thomasfredericks/Mozard/extras/Max (Cycling '74)/Control Mozard with MIDI through serial.png

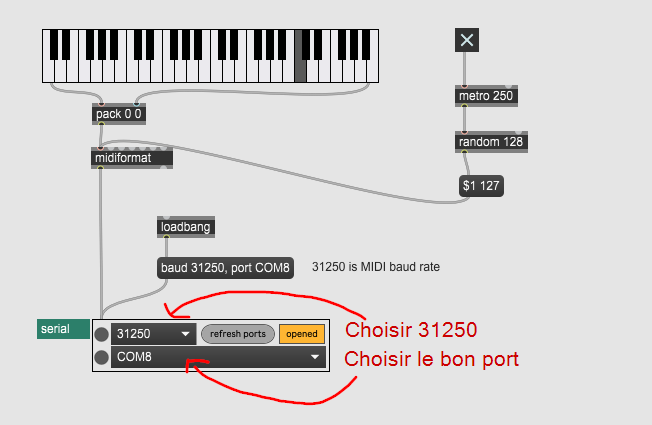
extras/Max (Cycling '74)/Control Mozard with MIDI through serial.png
