thomasfredericks/Mozard/src/Mozard.h

// ATMEL ATMEGA8 & 168 / ARDUINO
//
//                  +-\/-+
//            PC6  1|    |28  PC5 (AI 5)
//      (D 0) PD0  2|    |27  PC4 (AI 4)
//      (D 1) PD1  3|    |26  PC3 (AI 3)
//      (D 2) PD2  4|    |25  PC2 (AI 2)
// PWM+ (D 3) PD3  5|    |24  PC1 (AI 1)
//      (D 4) PD4  6|    |23  PC0 (AI 0)
//            VCC  7|    |22  GND
//            GND  8|    |21  AREF
//            PB6  9|    |20  AVCC
//            PB7 10|    |19  PB5 (D 13)
// PWM+ (D 5) PD5 11|    |18  PB4 (D 12)
// PWM+ (D 6) PD6 12|    |17  PB3 (D 11) PWM
//      (D 7) PD7 13|    |16  PB2 (D 10) PWM
//      (D 8) PB0 14|    |15  PB1 (D 9) PWM
//                  +----+
//


// POTS
// A1, A6, A7

// PIANO PADS
// A5, A4, A3, A2, D12, D11, D8, D7, D6, D5, D4, D3

// BUTTON 
// D2

/*
    IMPORTANT: Mozard requires mozzi_config.h to be
    be changed from STANDARD mode to HIFI.
    In Mozz/mozzi_config.h, change
    #define AUDIO_MODE STANDARD
    //#define AUDIO_MODE HIFI
    to
    //#define AUDIO_MODE STANDARD
    #define AUDIO_MODE HIFI

*/

#ifndef MOZARD_TOUCH_SENSITIVITY
#define MOZARD_TOUCH_SENSITIVITY 2
#endif


// powers of 2 please
#define CONTROL_RATE 256

#include <mozzi_midi.h>
/*
#ifndef NOMIDI

#include <MIDI.h>
MIDI_CREATE_DEFAULT_INSTANCE();

#endif
*/

#include "MozziGuts.h"
#include "mozzi_rand.h"

#include "MozardMidi.h"


class MozardNano {

  public:

    /*
        int findHighestKeyHeld() {
          int key = -1;
          for ( uint8_t i = 0; i < 12; i++ ) {
            if ( keys[i] > 0 ) key = i;
          }
          return key;
        }
    */
  private:

    MozardMidi midi = MozardMidi(&Serial);
   

    bool keys[14]; // 12 keys + 2 buttons

    uint8_t keyPins[14] = {A5, A4, A3, A2, 12, 11, 8, 7, 6, 5, 4, 3,2,A0};
    uint8_t thresholds[14] = {0, 0, 0, 0, 0, 0, 0, 0, 0, 0, 0, 0, 0,0};
    uint8_t keyIndex = 0;
    uint8_t keyJustPressed = 0;
    uint8_t keyJustReleased = 0;
    uint8_t buttonJustPressed = 0;

    char octave = 5;

    byte analogReading = 0;
    #define MOZARD_ANALOG_PINS 3
    int analogValues[MOZARD_ANALOG_PINS];
    byte analogPins[MOZARD_ANALOG_PINS] = {6,7,1}; // A, B, C
    /*
    void (*noteOnCallback)(byte note, byte velocity);
    void (*noteOffCallback)(byte note, byte velocity);
    void (*controlChangeCallback)(byte controller, byte value);
    */
    void (*keyPressedCallback)(byte key);
    void (*keyReleasedCallback)(byte key);
    void (*buttonLeftPressedCallback)(void);
    void (*buttonRightPressedCallback)(void);

    uint8_t readCapacitivePin(int pinToMeasure) {
      // Variables used to translate from Arduino to AVR pin naming
      volatile uint8_t* port;
      volatile uint8_t* ddr;
      volatile uint8_t* pin;
      // Here we translate the input pin number from
      //  Arduino pin number to the AVR PORT, PIN, DDR,
      //  and which bit of those registers we care about.
      byte bitmask;
      port = portOutputRegister(digitalPinToPort(pinToMeasure));
      ddr = portModeRegister(digitalPinToPort(pinToMeasure));
      bitmask = digitalPinToBitMask(pinToMeasure);
      pin = portInputRegister(digitalPinToPort(pinToMeasure));



      // Discharge the pin first by setting it low and output
      *port &= ~(bitmask);
      *ddr  |= bitmask;

      asm("nop");           // delay(1);

      // noInterrupts();

      // Prevent the timer IRQ from disturbing our measurement
      //noInterrupts();
      // Make the pin an input with the internal pull-up on
      *ddr &= ~(bitmask);
      *port |= bitmask;

      // Now see how long the pin to get pulled up. This manual unrolling of the loop
      // decreases the number of hardware cycles between each read of the pin,
      // thus increasing sensitivity.
      uint8_t cycles = 8;
      if      (*pin & bitmask) {
        cycles =  0;
      }
      else if (*pin & bitmask) {
        cycles =  1;
      }
      else if (*pin & bitmask) {
        cycles =  2;
      }
      else if (*pin & bitmask) {
        cycles =  3;
      }
      else if (*pin & bitmask) {
        cycles =  4;
      }
      else if (*pin & bitmask) {
        cycles =  5;
      }
      else if (*pin & bitmask) {
        cycles =  6;
      }
      else if (*pin & bitmask) {
        cycles =  7;
      }/*
      else if (*pin & bitmask) {
        cycles =  8;
      }
      else if (*pin & bitmask) {
        cycles =  9;
      }
      else if (*pin & bitmask) {
        cycles = 10;
      }
      else if (*pin & bitmask) {
        cycles = 11;
      }
      else if (*pin & bitmask) {
        cycles = 12;
      }
      else if (*pin & bitmask) {
        cycles = 13;
      }
      else if (*pin & bitmask) {
        cycles = 14;
      }
      else if (*pin & bitmask) {
        cycles = 15;
      }
      else if (*pin & bitmask) {
        cycles = 16;
      }
*/
      // End of timing-critical section
      // interrupts();

      // Discharge the pin again by setting it low and output
      //  It's important to leave the pins low if you want to
      //  be able to touch more than 1 sensor at a time - if
      //  the sensor is left pulled high, when you touch
      //  two sensors, your body will transfer the charge between
      //  sensors.
      *port &= ~(bitmask);
      *ddr  |= bitmask;

      return cycles ;
    }


// http://hinton-instruments.co.uk/reference/midi/protocol/index.htm
// https://www.midi.org/specifications-old/item/table-1-summary-of-midi-message    
/*
#define MM_NOTE_OFF 0x08
#define MM_NOTE_ON 0x09
#define MM_CTL 0x0B
 byte  midiType;
 uint8_t midiMessageLength = 0;
 byte midiMessage[3];
*/

  public:
   void loop() {
		
		audioHook();

    midi.receiveMessages();

    // READ MIDI DATA
/*
    while ( Serial.available() ) {
      byte extracted = Serial.read();
      if (extracted < 0x80) {
        if ( midiType ) {
          midiMessage[midiMessageLength] = extracted;
          midiMessageLength++;
          if ( midiMessageLength == 2 ) {
            if ( midiType == MM_NOTE_OFF && noteOffCallback  ) {
              noteOffCallback(midiMessage[0],midiMessage[1] );
            } else if ( midiType == MM_NOTE_ON && noteOnCallback  ) {
              if ( midiMessage[1] == 0 ) noteOffCallback(midiMessage[0],midiMessage[1] );
              else noteOnCallback(midiMessage[0],midiMessage[1] );
            } else if ( midiType == MM_CTL && controlChangeCallback) {
              controlChangeCallback(midiMessage[0],midiMessage[1] );
            }
            midiType = 0;
          }
        }
      } else {
        // GET RID OF CHANNEL DATA
        extracted = extracted >> 4;
        // ONLY HANDLE KNOWN MESSAGES
        if ( extracted == MM_NOTE_OFF || extracted == MM_NOTE_ON || extracted == MM_CTL ) {
            midiType = extracted;
        } else {
            midiType = 0;
        }
        midiMessageLength = 0;
      }
    }
*/


   }

    void setup() {
      
      startMozzi(CONTROL_RATE);

      reconnectDigitalIn  ( 0 ) ;
      reconnectDigitalIn  ( 2 ) ;
      reconnectDigitalIn  ( 3 ) ;
      reconnectDigitalIn  ( 4 ) ;
      reconnectDigitalIn  ( 5 ) ;

      randSeed(); // reseed the random generator for different results each time the sketch runs

     
      for ( byte i = 0 ; i <  MOZARD_ANALOG_PINS ; i++ ) {
        analogValues[i] = mozziAnalogRead(analogPins[i]);
      }

/*

      #ifndef NOMIDI
	  // Initiate MIDI communications, listen to all channels
	  MIDI.begin(MIDI_CHANNEL_OMNI);
	  #else
	  Serial.begin(57600);
	  #endif
      */
      Serial.begin(31250);
    }


   void setControlChangeCallback(void (*fptr)(byte channel,byte controller, byte value)) {
      midi.setControlChangeCallback(fptr);
     //controlChangeCallback = fptr;
    }

    void setMidiNoteOnCallback(void (*fptr)(byte channel,byte note, byte velocity)) {
     //noteOnCallback = fptr;
      midi.setMidiNoteOnCallback(fptr);
    }

     void setMidiNoteOffCallback(void (*fptr)(byte channel,byte note)) {
      //noteOffCallback = fptr;
      midi.setMidiNoteOffCallback(fptr);
    }
/*
   // void MIDI_Class::setHandlePitchBend 	( 	void(*)(byte channel, int bend)  	fptr	) 	
     void setPitchBendCallback(void (*fptr)(byte channel, int bend) ) {
      #ifndef NOMIDI
      MIDI.setHandlePitchBend(fptr);  // Put only the name of the function
      #endif
    } 

      */
  // void setHandleNoteOn(void (*fptr)(byte channel, byte note, byte velocity));
  //  keyPressedCallback               = fptr; 
    void setKeyPressedCallback(void (*fptr)(byte key)) {
     
      keyPressedCallback = fptr;

    }


     void setKeyReleasedCallback(void (*fptr)(byte key)) {
     
      keyReleasedCallback = fptr;

    }

     void setButtonLeftPressedCallback(void (*fptr)(void)) {
     	buttonLeftPressedCallback = fptr;
     }

    void setButtonRightPressedCallback (void (*fptr)(void)){
    	buttonRightPressedCallback = fptr;
    }




protected:


    bool aKeyIsPressed() {
      return keyJustPressed > 0;
    }

    bool aKeyIsReleased() {
      return keyJustReleased > 0;
    }

    uint8_t getKeyPressed() {
    	return keyJustPressed;
    }

     uint8_t getKeyReleased() {
    	return keyJustReleased;
    }


    uint8_t getNotePressed() {
      return keyToNote(keyJustPressed);
    }

    uint8_t getNoteReleased() {
      return keyToNote(keyJustReleased);
    }

    bool buttonAPressed() {
      return buttonJustPressed == 1;
    }

    bool buttonBPressed() {
      return buttonJustPressed == 2;
    }


public:

    uint8_t  getKeyPressedCount() {
      uint8_t keyCount = 0;
      for ( uint8_t i =0; i < 12; i++) {
        if (keys[i] == 1) keyCount = keyCount + 1;
      }
      return keyCount;
    }

	uint8_t  keyToNote(uint8_t  key) {
    	return octave * 12 + key -1;
    }
  

  uint8_t  noteToKey(byte  note) {
      return (note % 12) + 1; 
  }

	int getTopLeftPotentiometer() {
      return analogValues[0];
    }    
    
    int getBottomLeftPotentiometer() {
      return analogValues[1];
    }

     int getRightPotentiometer() {
      return analogValues[2];
    }

    void setOctave( char newOctave) {
      octave = constrain(newOctave, 0, 11);
    }

    void octaveUp() {
      setOctave(octave + 1);
    }

    void octaveDown() {
      setOctave(octave - 1);
    }

  void updateControl() {



      analogValues[analogReading] = mozziAnalogRead(analogPins[analogReading]);
      analogReading = ( analogReading + 1 ) % MOZARD_ANALOG_PINS;
      

      keyJustPressed = keyJustReleased = 0;
      buttonJustPressed = 0;
      
      uint8_t capacitance = readCapacitivePin(keyPins[keyIndex]);
      boolean pressed = capacitance > MOZARD_TOUCH_SENSITIVITY;
      //Serial.print(keyIndex);
      //Serial.write(32);
     // Serial.println(capacitance);
      


      if ( pressed ) {
        if ( keys[keyIndex] == 0 ) {
          if ( keyIndex < 12 ) keyJustPressed = keyIndex + 1;
          else buttonJustPressed = keyIndex - 11;
        }
        keys[keyIndex] = 1;
      } else {
        if ( keys[keyIndex] == 1 ) {
          if ( keyIndex < 12 ) keyJustReleased = keyIndex + 1;
        }
        keys[keyIndex] = 0;
      }


      keyIndex = (keyIndex + 1) % 14; // 12 keys + 2 buttons

      if ( aKeyIsPressed() && keyPressedCallback ) keyPressedCallback(getKeyPressed());
      else if ( aKeyIsReleased() && keyReleasedCallback ) keyReleasedCallback(getKeyReleased());
      else if ( buttonBPressed() && buttonLeftPressedCallback ) buttonLeftPressedCallback();
      else if ( buttonAPressed() && buttonRightPressedCallback ) buttonRightPressedCallback();

    }


};

MozardNano Mozard;
